splash5/nisetro_wsc/preview/windows/Resource.h

//{{NO_DEPENDENCIES}}
// Microsoft Visual C++ generated include file.
// Used by NisetroPreviewSDL.rc
//
#define ID_STATUSBAR                    101
#define IDS_APP_TITLE                   102
#define IDD_ABOUTBOX                    103
#define IDI_NISETROPREVIEWSDL           107
#define IDI_SMALL                       108
#define IDC_NISETROPREVIEWSDL           109
#define ID_MENU_NISETROPREVIEWSDL       110
#define ID_ACCEL_NISETROPREVIEWSDL      113
#define ID_MENU_FILE_EXIT               32000
#define ID_MENU_FILE_SCREENSHOT         32100
#define ID_MENU_OPTIONS_VIDEO_SIZE_X1   32200
#define ID_MENU_OPTIONS_VIDEO_SIZE_X2   32201
#define ID_MENU_OPTIONS_VIDEO_SIZE_X3   32202
#define ID_MENU_OPTIONS_VIDEO_SIZE_X4   32203
#define ID_MENU_OPTIONS_VIDEO_SIZE_X5   32204
#define ID_MENU_OPTIONS_VIDEO_ROTATE_AUTO 32205
#define ID_MENU_OPTIONS_VIDEO_ROTATE_VERTICAL 32206
#define ID_MENU_OPTIONS_VIDEO_ROTATE_HORIZONTAL 32207
#define ID_MENU_OPTIONS_VIDEO_ROTATE_KERORICAN 32208
#define ID_MENU_OPTIONS_VIDEO_SHOW_LCD_SEGMENTS 32209
#define ID_MENU_OPTIONS_VIDEO_FULLSCREEN 32210
#define ID_MENU_OPTIONS_VIDEO_BACKBUFFER_SIZE_X1 32211
#define ID_MENU_OPTIONS_VIDEO_BACKBUFFER_SIZE_X2 32212
#define ID_MENU_OPTIONS_VIDEO_BACKBUFFER_SIZE_X3 32213
#define ID_MENU_OPTIONS_VIDEO_BACKBUFFER_SIZE_X4 32214
#define ID_MENU_OPTIONS_VIDEO_BACKBUFFER_SIZE_X5 32215
#define ID_MENU_OPTIONS_VIDEO_TEXTURESCALE_NEAREST 32216
#define ID_MENU_OPTIONS_VIDEO_TEXTURESCALE_LINEAR 32217
#define ID_MENU_OPTIONS_VIDEO_TEXTURESCALE_BEST 32218
#define ID_MENU_OPTIONS_VIDEO_TEXTUREFILTER_NEAREST 32219
#define ID_MENU_OPTIONS_VIDEO_TEXTUREFILTER_LINEAR 32220
#define ID_MENU_OPTIONS_VIDEO_TEXTUREFILTER_BEST 32221
#define ID_MENU_OPTIONS_AUDIO_ENABLEINTERPOLATION 32300
#define ID_MENU_OPTIONS_AUDIO_MUTEAUDIO 32301
#define ID_MENU_OPTIONS_USB_DEVICEID_0  32400
#define ID_MENU_OPTIONS_USB_DEVICEID_1  32401
#define ID_MENU_OPTIONS_USB_DEVICEID_2  32402
#define ID_MENU_OPTIONS_USB_DEVICEID_3  32403
#define ID_MENU_OPTIONS_USB_DEVICEID_4  32404
#define ID_MENU_OPTIONS_USB_DEVICEID_5  32405
#define ID_MENU_OPTIONS_USB_DEVICEID_6  32406
#define ID_MENU_OPTIONS_USB_DEVICEID_7  32407
#define ID_MENU_OPTIONS_USB_DEVICEID_8  32408
#define ID_MENU_OPTIONS_USB_DEVICEID_9  32409
#define ID_MENU_HELP_ABOUT              32900
#define IDC_STATIC                      -1

// Next default values for new objects
// 
#ifdef APSTUDIO_INVOKED
#ifndef APSTUDIO_READONLY_SYMBOLS
#define _APS_NO_MFC                     1
#define _APS_NEXT_RESOURCE_VALUE        117
#define _APS_NEXT_COMMAND_VALUE         32107
#define _APS_NEXT_CONTROL_VALUE         1000
#define _APS_NEXT_SYMED_VALUE           112
#endif
#endif
