splash5/nisetro_wsc/preview/windows/stdafx.cpp

// stdafx.cpp : source file that includes just the standard includes
// NisetroPreviewSDL.pch will be the pre-compiled header
// stdafx.obj will contain the pre-compiled type information

#include "stdafx.h"

// TODO: reference any additional headers you need in STDAFX.H
// and not in this file
